hojadurdy/Flux_Capacitor_Mini/Images/GIF/0-1.gif

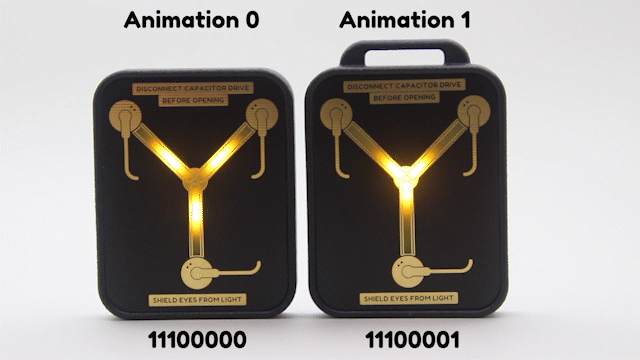
Images/GIF/0-1.gif
